midilab/aciduino/v2/docs/images/AciduinoScreens.jpg

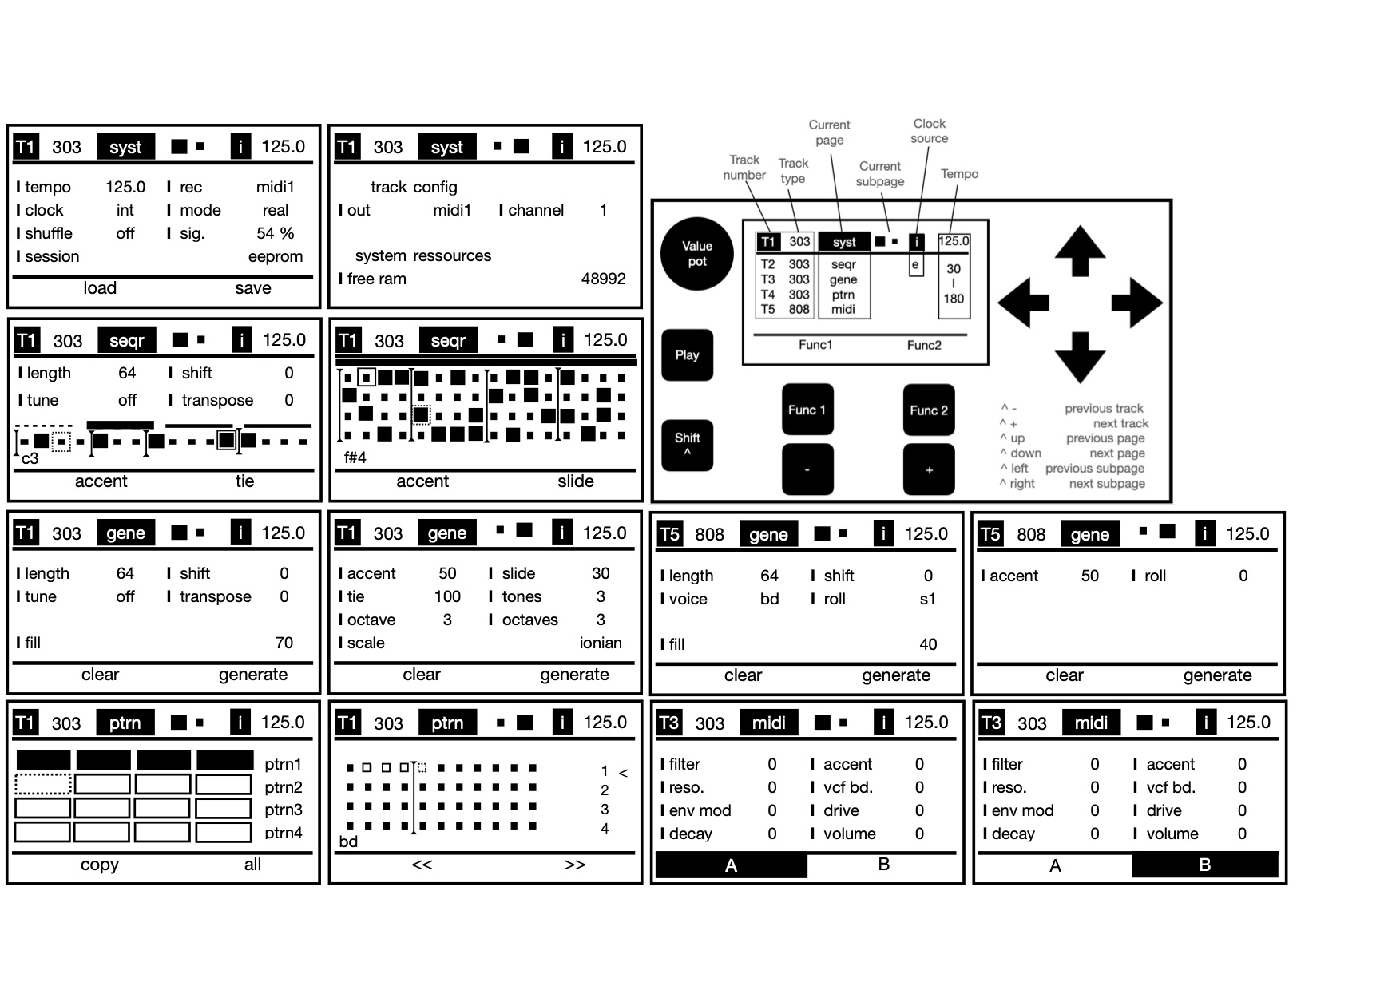
v2/docs/images/AciduinoScreens.jpg
