midilab/aciduino/v2/docs/images/BasicControls.png

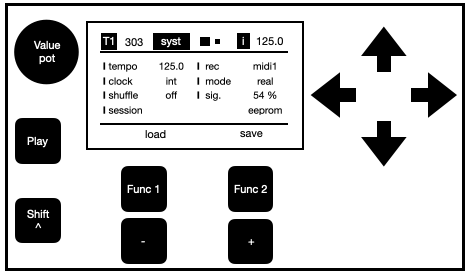
v2/docs/images/BasicControls.png
