midilab/aciduino/v2/hardware/HugoEscalpelo-3DCase-1.3inOLED-ESP32DevKitV1/Circuit/Schematic.png

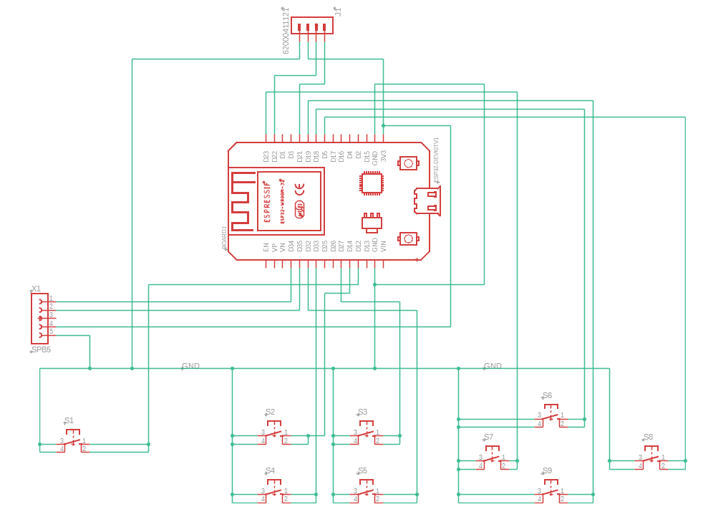
v2/hardware/HugoEscalpelo-3DCase-1.3inOLED-ESP32DevKitV1/Circuit/Schematic.png
