midilab/aciduino/v2/hardware/HugoEscalpelo-3DCase-1.3inOLED-ESP32DevKitV1/img/90x150mm-universal-pcb.jpg

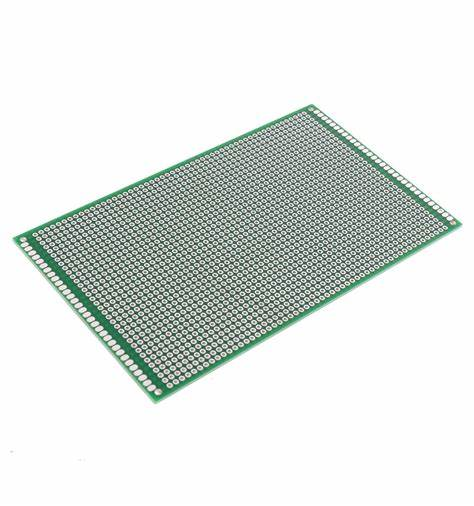
v2/hardware/HugoEscalpelo-3DCase-1.3inOLED-ESP32DevKitV1/img/90x150mm-universal-pcb.jpg
