midilab/aciduino/v2/hardware/HugoEscalpelo-3DCase-1.3inOLED-ESP32DevKitV1/img/ESP32 DevKit V1.jpg

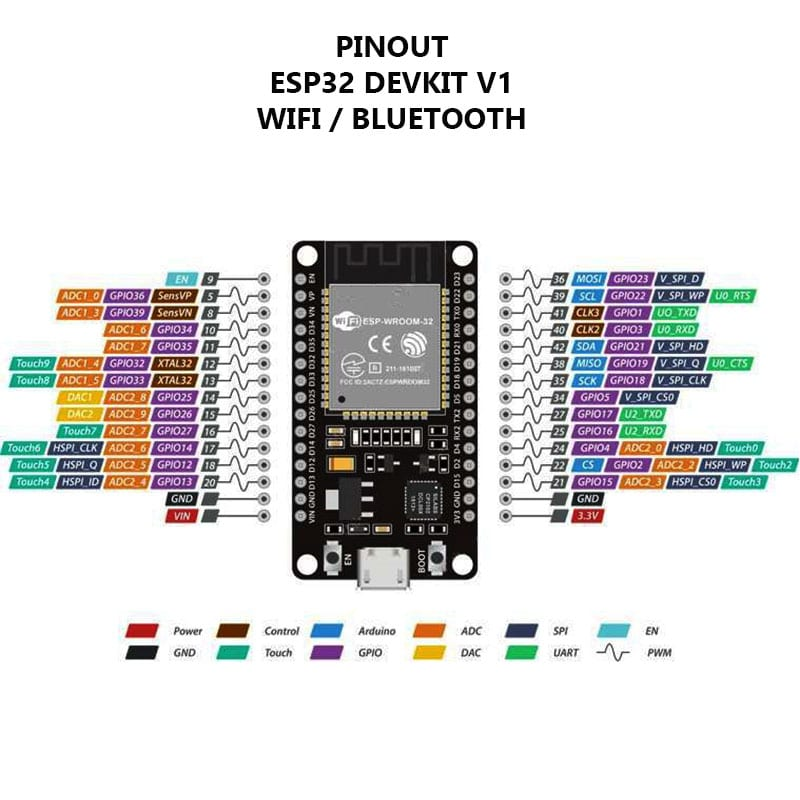
v2/hardware/HugoEscalpelo-3DCase-1.3inOLED-ESP32DevKitV1/img/ESP32 DevKit V1.jpg
