midilab/aciduino/v2/hardware/HugoEscalpelo-3DCase-1.3inOLED-ESP32DevKitV1/img/Female-heade-4pin.jpg

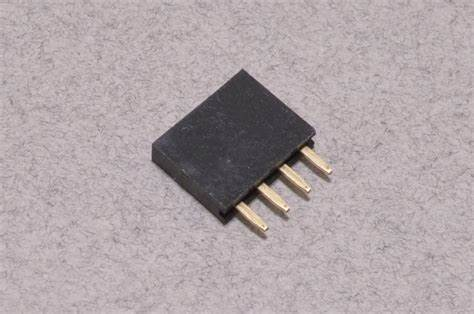
v2/hardware/HugoEscalpelo-3DCase-1.3inOLED-ESP32DevKitV1/img/Female-heade-4pin.jpg
