midilab/aciduino/v2/hardware/HugoEscalpelo-3DCase-1.3inOLED-ESP32DevKitV1/img/Keyes-rotary-encoder.jpg

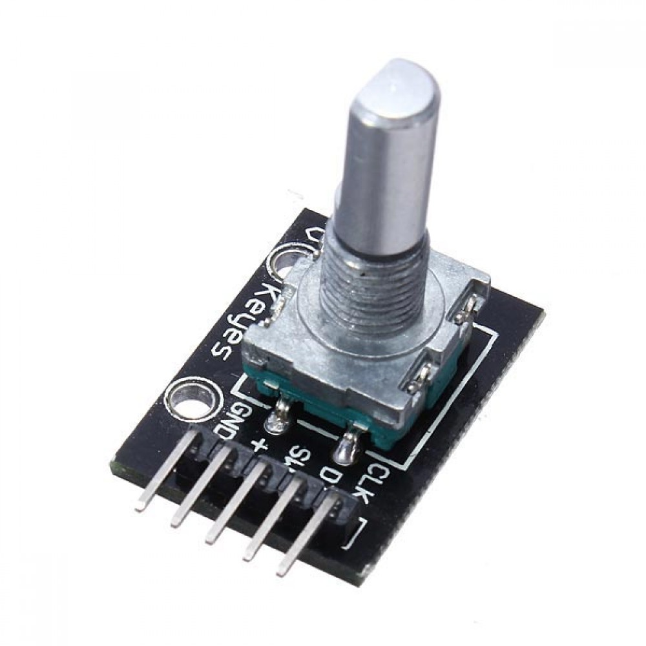
v2/hardware/HugoEscalpelo-3DCase-1.3inOLED-ESP32DevKitV1/img/Keyes-rotary-encoder.jpg
