midilab/aciduino/v2/hardware/HugoEscalpelo-3DCase-2.4inOLED-ESP32DevKitV1/img/2.14in-i2c-128x64-oled.png

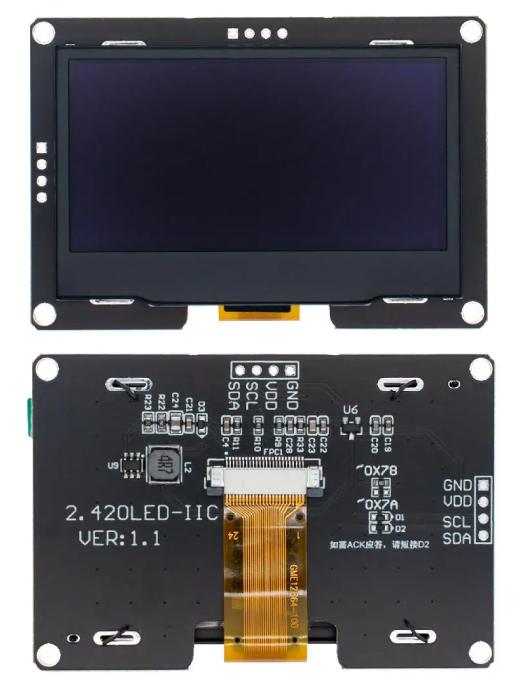
v2/hardware/HugoEscalpelo-3DCase-2.4inOLED-ESP32DevKitV1/img/2.14in-i2c-128x64-oled.png
