midilab/aciduino/v2/hardware/HugoEscalpelo-3DCase-2.4inOLED-ESP32DevKitV1/img/M2x8-screw.jpg

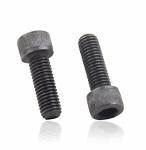
v2/hardware/HugoEscalpelo-3DCase-2.4inOLED-ESP32DevKitV1/img/M2x8-screw.jpg
