midilab/aciduino/v2/hardware/imgs/aciduinov2-lite-uone.jpg

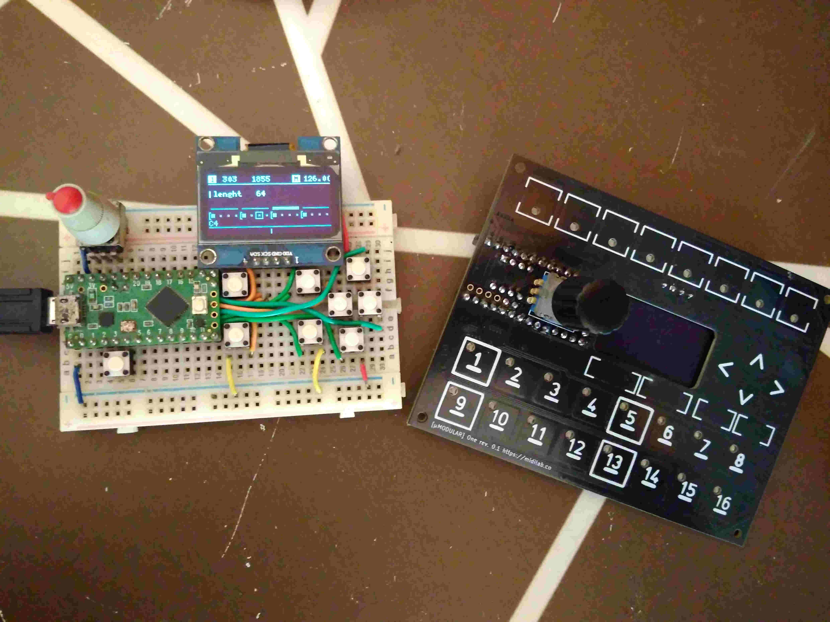
v2/hardware/imgs/aciduinov2-lite-uone.jpg
