midilab/aciduino/v2/hardware/imgs/aciduinov2-lite.jpg

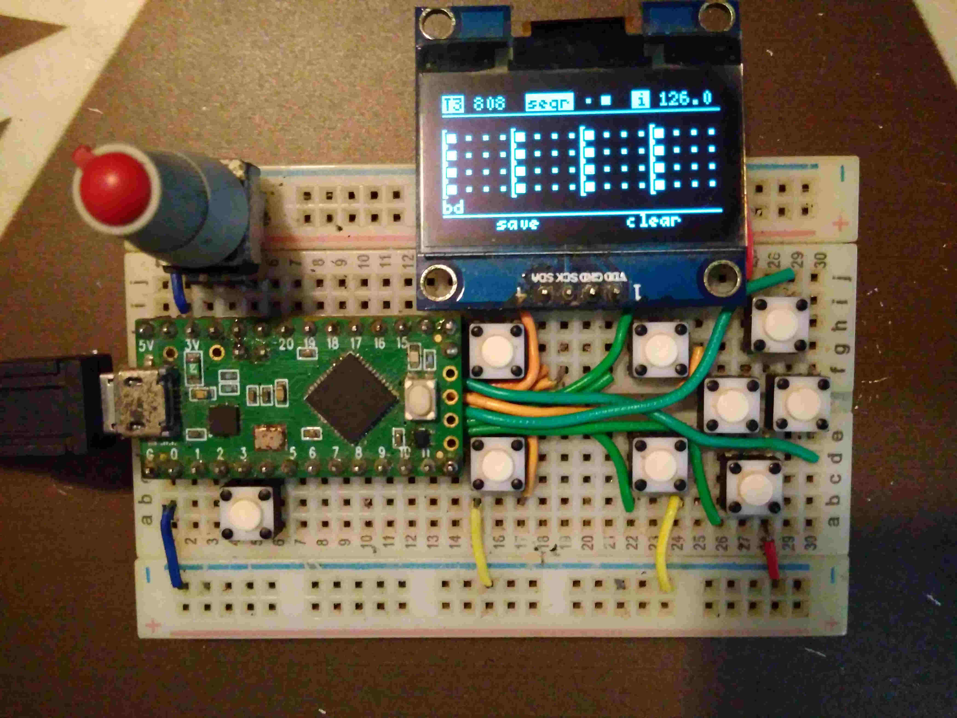
v2/hardware/imgs/aciduinov2-lite.jpg
