midilab/aciduino/v2/hardware/HugoEscalpelo-3DCase-2.4inOLED-ESP32DevKitV1/Assembly/IMG_20240221_184632.jpg

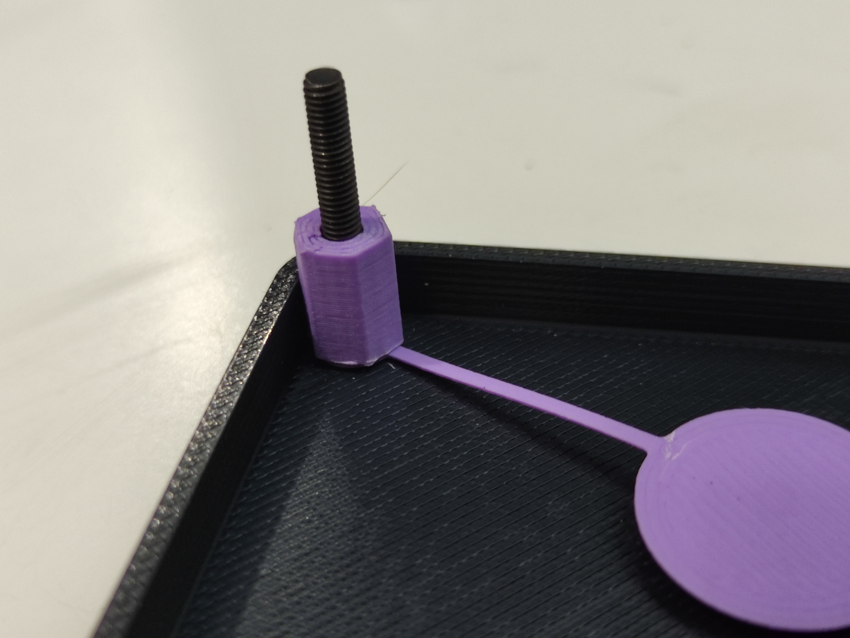
v2/hardware/HugoEscalpelo-3DCase-2.4inOLED-ESP32DevKitV1/Assembly/IMG_20240221_184632.jpg
