midilab/aciduino/v2/hardware/HugoEscalpelo-3DCase-1.3inOLED-ESP32DevKitV1/Circuit/Aciduino_Schematic_v6.sch

## EAGLE design v2/hardware/HugoEscalpelo-3DCase-1.3inOLED-ESP32DevKitV1/Circuit/Aciduino_Schematic_v6.sch (2024-02-22)

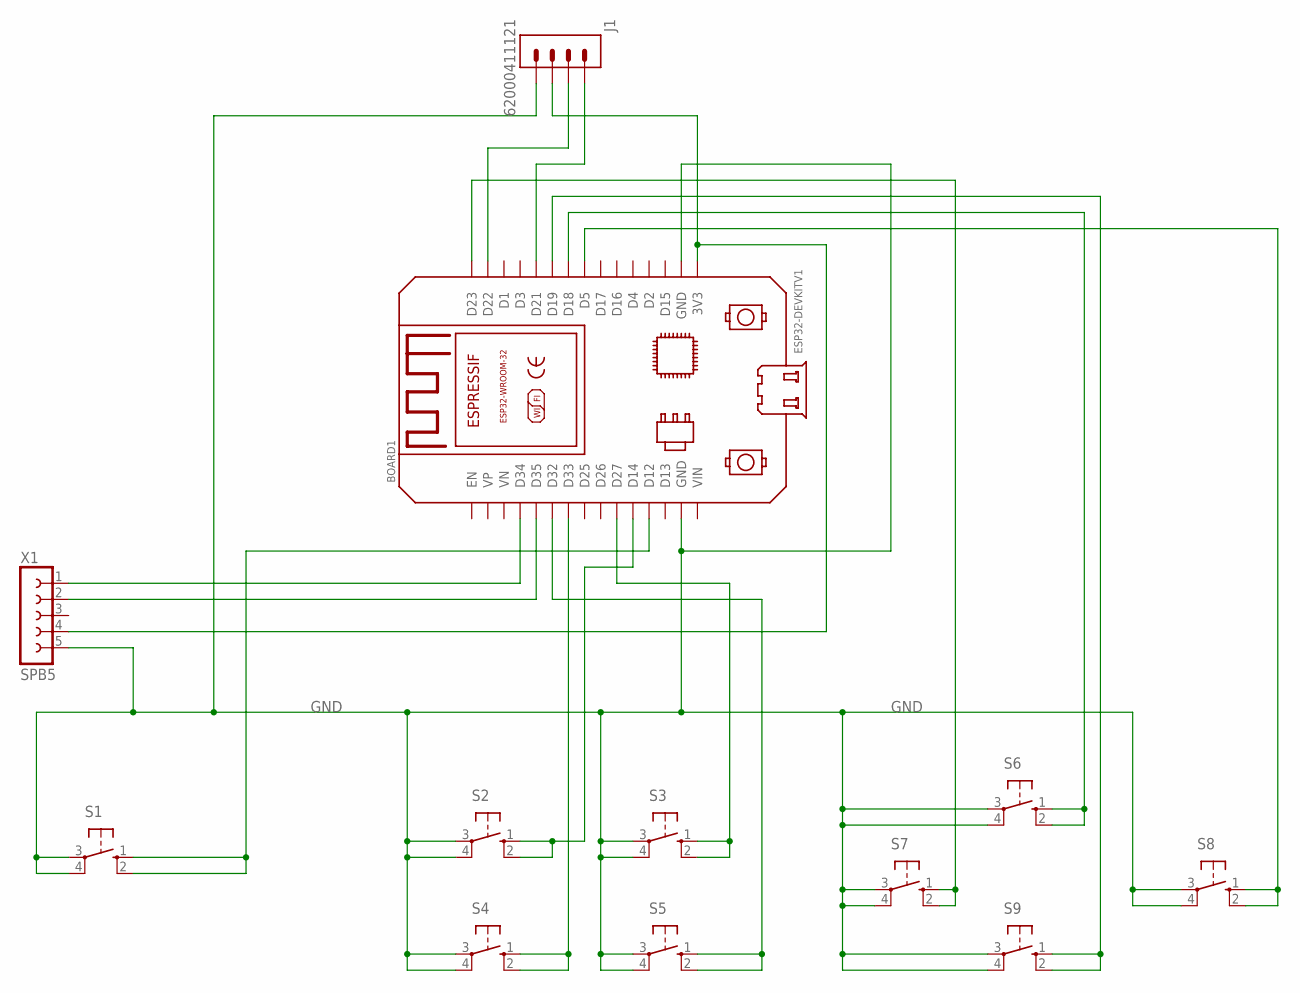
[picture p61: schematic Aciduino_Schematic_v6.sch]

Parts:
BOARD1: ESP32DEVKITV1SHRIDATTDUDHAT; ESP32-DEVKITV1
J1: 62000411121
S1, S2, S3, S4, S5, S6, S7, S8, S9: 10-XX; B3F-10XX
X1: SPB5

Connections:
GND: BOARD1.GND, BOARD1.GND@1 (GND), J1.4, S1.3, S1.4 (P1), S2.3, S2.4 (P1), S3.3, S3.4 (P1), S4.3, S4.4 (P1), S5.3, S5.4 (P1), S6.3, S6.4 (P1), S7.3, S7.4 (P1), S8.3, S8.4 (P1), S9.3, S9.4 (P1), X1.5
unnamed: BOARD1.D12, S1.1 (S), S1.2 (S1)
unnamed: BOARD1.D14, S2.1 (S), S2.2 (S1)
unnamed: BOARD1.D21, J1.1
unnamed: BOARD1.D27, S3.1 (S), S3.2 (S1)
unnamed: BOARD1.D33, S4.1 (S), S4.2 (S1)
unnamed: BOARD1.D32, S5.1 (S), S5.2 (S1)
unnamed: BOARD1.D5, S8.1 (S), S8.2 (S1)
unnamed: BOARD1.D18, S6.1 (S), S6.2 (S1)
unnamed: BOARD1.D19, S9.1 (S), S9.2 (S1)
unnamed: BOARD1.D23, S7.1 (S), S7.2 (S1)
unnamed: BOARD1.3V3, J1.3, X1.4
unnamed: BOARD1.D34, X1.1
unnamed: BOARD1.D35, X1.2
unnamed: BOARD1.D22, J1.2
