midilab/aciduino/v2/AciduinoV2/src/aciduino.cpp

#include "aciduino.hpp"

//
// setup and runtime
//
void Aciduino::init() {
  // setup clock system
  uClockSetup();
  // init the sequencer
  initSequencer();

  // force initializatiron of mute pattern data
  for (uint8_t i=0; i < 4; i++) {
    for (uint8_t j=0; j < TRACK_NUMBER_808; j++) {
      _mute_grid[i].map_808[j] = 0xFFFF;
    }
  }
}

void Aciduino::run() {
  // let uCtrl do his job
  uCtrl.run();
}

//
// Sequencer initialization
//
void Aciduino::initSequencer()
{
  // storage setup epprom/sdcard
  storageSetup();

  // init default track output data
  for(uint8_t track=0; track < TRACK_NUMBER_303+TRACK_NUMBER_808; track++) {
    _track_output_setup[track].output = MIDI_OUTPUT;
    _track_output_setup[track].channel = track;
    _track_output_setup[track].port = 0;
  }
  
  // the acid sequencer main output callback
  aciduino.seq.setOutputCallback(sequencerOutHandler);

  // we're going to init epprom in two cases:
  // if track layout changes || if no aciduino data present at epprom
  // so if you want to keep your pattenrs and change layout consider backup pattenrs into another sequencer
  // because they will be wipeout for the new memory layout to take place
  if (checkEppromDataLayoutChange()) {
    eppromInit();
  }

  // load shuffle form memory pattern?
  int8_t init_template[2] = {0,0};
  uClock.setShuffleTemplate(init_template, 2);

  // load epprom saved session
  loadSession();
  // load first pattern
  loadPattern(0);
}

void Aciduino::uClockSetup()
{
  // Inits the clock
  uClock.init();
  
  // Set the callback function for the step sequencer on 96PPQN and for step sequencer feature
  uClock.setOnPPQN(Aciduino::onPPQNCallback);
  uClock.setOnStep(Aciduino::onStepCallback);
  // Set the callback function for the clock output to send MIDI Sync message.
  uClock.setOnSync24(Aciduino::onSync24Callback);
  // Set the callback function for MIDI Start and Stop messages.
  uClock.setOnClockStart(Aciduino::onClockStart);  
  uClock.setOnClockStop(Aciduino::onClockStop);
  
  // Set the clock BPM to 126 BPM
  uClock.setTempo(126);
  //uClock.setMode(uClock.EXTERNAL_CLOCK);
}

void Aciduino::storageSetup()
{
  //
  // initiate epprom memory layout setup
  //
#if defined(ARDUINO_ARCH_ESP32) || defined(ESP32)
  _epprom_size = 4096;
#else
  _epprom_size = EEPROM.length();
#endif

  _epprom_check_data_address = 0;
  _epprom_session_address = 2;
  _epprom_session_size =(sizeof(_generative_303) + sizeof(_generative_808) + sizeof(_control_map_global) + sizeof(_track_output_setup));
  
  //
  // common pattern data definitions
  //
  _pattern_303_track_size = aciduino.seq.get303PatternTrackSize();
  _pattern_808_track_size = aciduino.seq.get808PatternTrackSize();
  _pattern_303_mem_size = aciduino.seq.get303PatternMemorySize();
  _pattern_808_mem_size = aciduino.seq.get808PatternMemorySize();
  _pattern_total_mem_size = (_pattern_303_mem_size + _pattern_808_mem_size + sizeof(_mute_grid));
  _eprrom_pattern_address = (_epprom_session_address + _epprom_session_size);
  _eprrom_pattern_available = (_epprom_size-_epprom_session_size-_epprom_session_address) / (_pattern_total_mem_size);
}

uint16_t Aciduino::getNumOfPatterns() {
  return _eprrom_pattern_available;
}

uint16_t Aciduino::getSessionSize() {
  return _epprom_session_size;
}

uint16_t Aciduino::getStorageSize() {
  return _epprom_size;
}

//
// Main interface
//
void Aciduino::playStop()
{
  if (aciduino.isPlaying())
    aciduino.stop();
  else
    aciduino.play();
}

void Aciduino::play()
{
  uClock.start();
}

void Aciduino::stop()
{
  uClock.stop();
}

void Aciduino::recToggle()
{
  aciduino.seq.setRecStatus(!aciduino.seq.getRecStatus());
}

void Aciduino::previousTrack()
{
  if (aciduino._selected_track == 0) {
    aciduino._selected_track = aciduino.seq.getTrackNumber() - 1;
  } else {
    aciduino._selected_track -= 1;
  }
}

void Aciduino::nextTrack()
{
  if (aciduino._selected_track == aciduino.seq.getTrackNumber() - 1) {
    aciduino._selected_track = 0;
  } else {
    aciduino._selected_track += 1;
  }
}

// 
// Pattern Grids
//
// MUTE GRID
uint8_t Aciduino::getMuteGridState(uint8_t mute_pattern, uint8_t track, uint8_t voice)
{
  // 303
  if (aciduino.seq.is303(track)) {
    return GET_BIT(_mute_grid[mute_pattern].map_303, track);
  // 808
  } else {
    return GET_BIT(_mute_grid[mute_pattern].map_808[track-TRACK_NUMBER_303], voice);
  }
}

void Aciduino::setMuteGridState(uint8_t mute_pattern, uint8_t state, uint8_t track, uint8_t voice)
{
  if (state == 0) {
    if (seq.is303(track)) {
      CLR_BIT(_mute_grid[mute_pattern].map_303, track);
    } else {
      CLR_BIT(_mute_grid[mute_pattern].map_808[track-TRACK_NUMBER_303], voice);
    }
  } else if (state == 1) {
    if (seq.is303(track)) {
      SET_BIT(_mute_grid[mute_pattern].map_303, track);
    } else {
      SET_BIT(_mute_grid[mute_pattern].map_808[track-TRACK_NUMBER_303], voice);
    }
  }
}
// PATTERN GRID
uint8_t Aciduino::getPatternGrid(uint8_t track)
{
  return _pattern_grid[track];
}

void Aciduino::setPatternGrid(uint8_t track, uint8_t pattern)
{
  _pattern_grid[track] = pattern;
}

//
// Generative
//
void Aciduino::generatePattern(int8_t track)
{
  uint8_t track_gen = track;
  if (track == -1)
    track_gen = _selected_track;

  if (seq.is303(track_gen)) 
    aciduino.seq.acidRandomize(track_gen, _generative_303[track_gen].generative_fill, _generative_303[track_gen].accent_probability, _generative_303[track_gen].slide_probability, _generative_303[track_gen].tie_probability, _generative_303[track_gen].number_of_tones, _generative_303[track_gen].lower_octave*12, _generative_303[track_gen].range_octave*12);
  else
    aciduino.seq.acidRandomize(track_gen, _generative_808[track_gen-TRACK_NUMBER_303].generative_fill, _generative_808[track_gen-TRACK_NUMBER_303].accent_probability, _generative_808[track_gen-TRACK_NUMBER_303].roll_probability);
}

uint8_t Aciduino::getGenerativeParam(uint8_t param, int8_t track)
{
  uint8_t track_change = track;
  uint8_t value = 0;
  if (track == -1)
    track_change = _selected_track;

  // TODO: make it array idx safe access between 303 and 808 state access
  switch (param) {
    case GENERATIVE_FILL:
      if (seq.is303(track_change)) 
        value = _generative_303[track_change].generative_fill;
      else
        value = _generative_808[track_change-TRACK_NUMBER_303].generative_fill; 
      break;
    case GENERATIVE_ACCENT:
      if (seq.is303(track_change)) 
        value = _generative_303[track_change].accent_probability;
      else
        value = _generative_808[track_change-TRACK_NUMBER_303].accent_probability; 
      break;
    case GENERATIVE_SLIDE:
      value = _generative_303[track_change].slide_probability;
      break;
    case GENERATIVE_TIE:
      value = _generative_303[track_change].tie_probability;
      break;
    case GENERATIVE_LOWER_OCTAVE:
      value = _generative_303[track_change].lower_octave;
      break;
    case GENERATIVE_RANGE_OCTAVE:
      value = _generative_303[track_change].range_octave;
      break;
    case GENERATIVE_NUM_TONES:
      value = _generative_303[track_change].number_of_tones;
      break;
    case GENERATIVE_ROLL:
      value = _generative_808[track_change-TRACK_NUMBER_303].roll_probability; 
      break;
    default:
      break;
  }

  return value;
}

void Aciduino::setGenerativeParam(uint8_t param, uint8_t data, int8_t track)
{
  uint8_t track_change = track;
  if (track == -1)
    track_change = _selected_track;

  switch (param) {
    case GENERATIVE_FILL:
      if (seq.is303(track_change))
        _generative_303[track_change].generative_fill = data;
      else
        _generative_808[track_change-TRACK_NUMBER_303].generative_fill = data;
      break;
    case GENERATIVE_ACCENT:
      if (seq.is303(track_change))
        _generative_303[track_change].accent_probability = data;
      else
        _generative_808[track_change-TRACK_NUMBER_303].accent_probability = data;
      break;
    case GENERATIVE_SLIDE:
      _generative_303[track_change].slide_probability = data;
      break;
    case GENERATIVE_TIE:
      _generative_303[track_change].tie_probability = data;
      break;
    case GENERATIVE_LOWER_OCTAVE:
      _generative_303[track_change].lower_octave = data;
      break;
    case GENERATIVE_RANGE_OCTAVE:
      _generative_303[track_change].range_octave = data;
      break;
    case GENERATIVE_NUM_TONES:
      _generative_303[track_change].number_of_tones = data;
      break;
    case GENERATIVE_ROLL:
        _generative_808[track_change-TRACK_NUMBER_303].roll_probability = data;
      break;
    default:
      break;
  }
}

//
// Track output setup
//
uint8_t Aciduino::getTrackOutputParam(uint8_t param, int8_t track)
{
  uint8_t track_change = track;
  if (track == -1)
    track_change = _selected_track;

  switch (param) {
    case TRACK_OUTPUT:
      return _track_output_setup[track_change].output;
    case TRACK_CHANNEL:
      return _track_output_setup[track_change].channel;
    case TRACK_PORT:
      return _track_output_setup[track_change].port;
    default:
      break;
  }
}

void Aciduino::setTrackOutputParam(uint8_t param, uint8_t data, int8_t track)
{
  uint8_t track_change = track;
  if (track == -1)
    track_change = _selected_track;

  switch (param) {
    case TRACK_OUTPUT:
      ATOMIC(_track_output_setup[track_change].output = data)
      break;
    case TRACK_CHANNEL:
      ATOMIC(_track_output_setup[track_change].channel = data)
      break;
    case TRACK_PORT:
      ATOMIC(_track_output_setup[track_change].port = data)
      break;
    default:
      break;
  }
}

//
// midi controller data accessors
//
int8_t Aciduino::getMidiControlParam(uint8_t param, uint8_t idx)
{
  switch (param) {
    case MIDI_CTRL:
      return _control_map_global[idx].ctrl;
    case MIDI_TRACK:
      return (int8_t)_control_map_global[idx].track;
    default:
      break;
  }
}

void Aciduino::setMidiControlParam(uint8_t param, int8_t data, uint8_t idx)
{
  switch (param) {
    case MIDI_CTRL:
      _control_map_global[idx].ctrl = data;
      break;
    case MIDI_TRACK:
      _control_map_global[idx].track = (uint8_t)data;
      break;
    default:
      break;
  }
}

//
// Midi utils
//
// 3 realtime messages used by uClock object inside interruption
inline void Aciduino::sendMidiClock() {
  msg_interrupt.type = uctrl::protocol::midi::Clock;
  uCtrl.midi->writeAllPorts(&msg_interrupt, 1);
}

void Aciduino::sendMidiStart() {
  msg.type = uctrl::protocol::midi::Start;
  uCtrl.midi->writeAllPorts(&msg, 0);  
}

void Aciduino::sendMidiStop() {
  msg.type = uctrl::protocol::midi::Stop;
  uCtrl.midi->writeAllPorts(&msg, 0);
}

// this is used inside interruption and outside, controlled by interrupted var
void Aciduino::sendMidiCC(uint8_t cc, uint8_t value, uint8_t channel, uint8_t port, uint8_t interrupted) {
  if (interrupted) {
    msg_interrupt_pots.type = uctrl::protocol::midi::ControlChange;
    msg_interrupt_pots.data1 = cc;
    msg_interrupt_pots.data2 = value;
    msg_interrupt_pots.channel = channel;
    uCtrl.midi->write(&msg_interrupt_pots, port+1, 1);
  } else {
    msg.type = uctrl::protocol::midi::ControlChange;
    msg.data1 = cc;
    msg.data2 = value;
    msg.channel = channel;
    uCtrl.midi->write(&msg, port+1, 0);
  }
}

void Aciduino::sendNote(uint8_t note, uint8_t channel, uint8_t port, uint8_t velocity) {
  msg.data1 = note;
  msg.data2 = velocity;
  msg.channel = channel;
  
  if (velocity == 0) {
    msg.type = uctrl::protocol::midi::NoteOff;
  } else {
    msg.type = uctrl::protocol::midi::NoteOn;
  }

  uCtrl.midi->write(&msg, port+1, 0);
}

// 
// storage schema
//
void Aciduino::loadSession()
{
  // check if there is a session saved.. otherwise init one based on the defaults
  // we can use the last byte as version control
  // load session data
  uCtrl.storage->load((void*)_generative_303, sizeof(_generative_303), _epprom_session_address);
  uCtrl.storage->load((void*)_generative_808, sizeof(_generative_808));
  uCtrl.storage->load((void*)_control_map_global, sizeof(_control_map_global));
  uCtrl.storage->load((void*)_track_output_setup, sizeof(_track_output_setup));
}

void Aciduino::saveSession()
{
  // save session data
  uCtrl.storage->save((void*)_generative_303, sizeof(_generative_303), _epprom_session_address);
  uCtrl.storage->save((void*)_generative_808, sizeof(_generative_808));
  uCtrl.storage->save((void*)_control_map_global, sizeof(_control_map_global));
  uCtrl.storage->save((void*)_track_output_setup, sizeof(_track_output_setup));
}

uint16_t Aciduino::getPatternEppromAddress(uint8_t pattern, int8_t track)
{
  uint16_t pattern_address = _eprrom_pattern_address + (pattern * _pattern_total_mem_size);
  if (track != -1) {
    pattern_address += aciduino.seq.is303(track) ? _pattern_303_track_size * track : _pattern_303_mem_size + (_pattern_808_track_size * (track-TRACK_NUMBER_303));
  }
  return pattern_address;
}

void Aciduino::loadPattern(uint8_t pattern, int8_t track, int8_t to_track)
{
  uint16_t pattern_address = 0;
  
  if (track != -1) {
    // load only a track patttern
    pattern_address = getPatternEppromAddress(pattern, track);
    
    // to_track request?
    if (to_track != -1)
      track = to_track;
      
    aciduino.seq.setMute(track, true);
    aciduino.seq.clearStackNote(track);
    uCtrl.storage->load((void*)aciduino.seq.getPatternData(track), (aciduino.seq.is303(track) ? _pattern_303_track_size : _pattern_808_track_size), pattern_address);
    aciduino.seq.setMute(track, false);

    // load _mute_grid only for track?
    //...
  } else {
    // load the whole pattern for all tracks
    pattern_address = getPatternEppromAddress(pattern);
    
    // mute all before load into memory(its volatile! here a mute is enongth)
    for (uint8_t i=0; i < (TRACK_NUMBER_303+TRACK_NUMBER_808); i++) {
      aciduino.seq.setMute(i, true);
    }
    // clear all floating notes around
    aciduino.seq.clearStackNote();
    
    // get 303 whole pattern data first
    uCtrl.storage->load((void*)aciduino.seq.getPatternData(0), _pattern_303_mem_size, pattern_address);
    // then 808 whole pattern data last
    uCtrl.storage->load((void*)aciduino.seq.getPatternData(TRACK_NUMBER_303), _pattern_808_mem_size, pattern_address+_pattern_303_mem_size);

    // load _mute_grid
    uCtrl.storage->load((void*)_mute_grid, sizeof(_mute_grid), pattern_address+_pattern_303_mem_size+_pattern_808_mem_size);
    
    // unmute all loaded fresh and new pattern
    for (uint8_t i=0; i < (TRACK_NUMBER_303+TRACK_NUMBER_808); i++) {
      aciduino.seq.setMute(i, false);
    }
  }
}

void Aciduino::savePattern(uint8_t pattern, int8_t track, int8_t from_track)
{
  uint16_t pattern_address = 0;
  if (track != -1) {
    // save only a track patttern
    pattern_address = getPatternEppromAddress(pattern, track);
    
    // to_track request?
    if (from_track != -1)
      track = from_track;
      
    uCtrl.storage->save((void*)aciduino.seq.getPatternData(track), (aciduino.seq.is303(track) ? _pattern_303_track_size : _pattern_808_track_size), pattern_address);

    // save _mute_grid for a specific patern
    //...
  } else {
    // saves the whole pattern for all tracks
    pattern_address = getPatternEppromAddress(pattern);
    // save 303 whole pattern data first
    uCtrl.storage->save((void*)aciduino.seq.getPatternData(0), _pattern_303_mem_size, pattern_address);
    // then 808 whole pattern data last
    uCtrl.storage->save((void*)aciduino.seq.getPatternData(TRACK_NUMBER_303), _pattern_808_mem_size, pattern_address+_pattern_303_mem_size);
    // _mute_grid data
    uCtrl.storage->save((void *)_mute_grid, sizeof(_mute_grid), pattern_address+_pattern_303_mem_size+_pattern_808_mem_size);
  }
}

void Aciduino::saveMuteGrid(uint8_t pattern)
{
  // _mute_grid data
  uCtrl.storage->save((void*)_mute_grid, sizeof(_mute_grid), getPatternEppromAddress(pattern)+_pattern_303_mem_size+_pattern_808_mem_size);
}

// copy current track data into same or another track pattern memory
void Aciduino::copyPattern(uint8_t pattern, int8_t track)
{
    _copy_pattern = pattern;
    _copy_track = track;
}

bool Aciduino::pastePattern(uint8_t pattern, int8_t track)
{
  bool copy_memory = true;
  
  if (track == -1 || _copy_track == - 1) {
    // paste whole pattern track per track
    for (uint8_t i=0; i < aciduino.seq.getTrackNumber(); i++) {
      // update _copy_track with current track
      _copy_track = i;
      pastePattern(pattern, i);
    }
    // paste _mute_grid too!
    uCtrl.storage->save((void*)_mute_grid, sizeof(_mute_grid), getPatternEppromAddress(pattern)+_pattern_303_mem_size+_pattern_808_mem_size);
    return true;
  }

  // check if track types are different
  if (aciduino.seq.is303(_copy_track) != aciduino.seq.is303(track)) {
    // cant copy.. handle UI
    return false;
  }
  
  // copy from memory or from storage?
  if (_pattern_grid[_copy_track] == _copy_pattern) {
    // we copy from current memory data
    copy_memory = true;
  } else {
    // we copy from storage data
    copy_memory = false;
  }

  // paste to memory or to storage?
  if (_pattern_grid[track] == pattern) {
    // TODO: should we save stuffs copied to memory?
    // we paste to current memory
    if (copy_memory) {
      // if paste is from memory to memory
      aciduino.seq.setMute(track, true);
      aciduino.seq.clearStackNote(track);
      memcpy(aciduino.seq.getPatternData(track), aciduino.seq.getPatternData(_copy_track), (aciduino.seq.is303(track) ? _pattern_303_track_size : _pattern_808_track_size));
      aciduino.seq.setMute(track, false);
    } else {
      // if paste is from storage to memory
      loadPattern(_copy_pattern, _copy_track, track);
    }
  } else {
    // we paste to storage data
    if (copy_memory) {
      // if paste is from memory to storage
      savePattern(pattern, track, _copy_track);
    } else {
      // if paste is from storage to storage
      uCtrl.storage->copy(getPatternEppromAddress(_copy_pattern, _copy_track), getPatternEppromAddress(pattern, track), (aciduino.seq.is303(track) ? _pattern_303_track_size : _pattern_808_track_size));
    }
  }

  return true;
}

/*
void Engine808::setBufferTrack(uint8_t track)
{
  // copy track into buffer
  memcpy(_track_helper_buffer, _sequencer[track], sizeof(_track_helper_buffer));
}
 */

bool Aciduino::checkEppromDataLayoutChange()
{
  uint16_t pattern_size = 0;
  uCtrl.storage->load((void*)&pattern_size, sizeof(pattern_size), _epprom_check_data_address);
  if (pattern_size == _pattern_total_mem_size) {
    return false;
  } else {
    return true;
  }
}

void Aciduino::eppromInit()
{
    uint16_t pattern_size = _pattern_total_mem_size;
    // init epprom session/pattern memory
    // init all epprom slots to defaults
    saveSession();
    for (uint8_t pattern=0; pattern < _eprrom_pattern_available; pattern++) {
      savePattern(pattern);
    }
    // mark epprom first bytes with pattern size to use as a checker for layout changes
    uCtrl.storage->save((void*)&pattern_size, sizeof(pattern_size), _epprom_check_data_address);
}

#if defined(TEENSYDUINO)
extern "C" char* sbrk(int incr);
int Aciduino::freeRam() {
  char top;
  return &top - reinterpret_cast<char*>(sbrk(0));
}
#elif defined(ARDUINO_ARCH_ESP32) || defined(ESP32)
int Aciduino::freeRam () 
{
  return ESP.getFreeHeap(); 
}
#elif defined(ARDUINO_ARCH_AVR)
int Aciduino::freeRam () 
{
  extern int __heap_start, *__brkval; 
  int v; 
  return (int) &v - (__brkval == 0 ? (int) &__heap_start : (int) __brkval); 
}
#endif

// used by aciduino.seq object as callback to spill data out
void Aciduino::sequencerOutHandler(uint8_t msg_type, uint8_t note, uint8_t velocity, uint8_t track)
{
  switch(aciduino._track_output_setup[track].output) {
    case MIDI_OUTPUT:
      aciduino.midiSequencerOutHandler(msg_type, note, velocity, aciduino._track_output_setup[track].channel, aciduino._track_output_setup[track].port);
      break;
    case CV_OUTPUT:
      // soon boy...
      break;
    case GATE_OUTPUT:
      // soooooooon...
      break;
  }
}

void Aciduino::midiSequencerOutHandler(uint8_t msg_type, uint8_t byte1, uint8_t byte2, uint8_t channel, uint8_t port)
{
  msg_interrupt.type = msg_type == NOTE_ON ? uctrl::protocol::midi::NoteOn : uctrl::protocol::midi::NoteOff;
  msg_interrupt.data1 = byte1;
  msg_interrupt.data2 = byte2;
  msg_interrupt.channel = channel;
  uCtrl.midi->write(&msg_interrupt, port+1, 1);
}

// All midi interface registred thru uCtrl get incomming data thru this callback
void Aciduino::midiInputHandler(uctrl::protocol::midi::MIDI_MESSAGE * msg, uint8_t port, uint8_t interrupted) 
{
  if ( uClock.getMode() == uClock.EXTERNAL_CLOCK ) {
    // external tempo control
    switch (msg->type) {
        case uctrl::protocol::midi::Clock:
          uClock.clockMe();
          return;
 
        case uctrl::protocol::midi::Start:
          uClock.start();
          return;
  
        case uctrl::protocol::midi::Stop:
          uClock.stop();
          return;
    }  
  }

  // control goes thru selected track(no matter what channel)
  switch (msg->type) {

    //
    // Note ON/OFF
    //  
    case uctrl::protocol::midi::NoteOn:
    case uctrl::protocol::midi::NoteOff:
      aciduino.seq.input(aciduino._selected_track, msg->type == uctrl::protocol::midi::NoteOn ? NOTE_ON : NOTE_OFF, msg->data1, msg->data2, interrupted);
      break;

    //
    // Control Change
    //
    case uctrl::protocol::midi::ControlChange:

      // CC MAP Control
      switch ( msg->data1 ) {

        // Sustain Controller 64
        case 64:
          //if (_foot_pedal_rec == true) {
          //  if ( msg->data2 == 127 ) {
              //footSwitchHandle(HIGH);
          //  } else if ( msg->data2 == 0 ) {
              //footSwitchHandle(LOW);
          //  }
          //  return;
          //}
          break;
      }
      break;
      
    default:
      break;
      
  }  
}

// a port to read midi notes 1ms
void Aciduino::midiHandle() {
  //while (uCtrl.midi->read(2)) {
  //}
  uCtrl.midi->read(aciduino._midi_rec_port, 1);
}

// used by uCtrl at 250us speed to get MIDI sync input messages on time
void Aciduino::midiHandleSync() {
  if (aciduino._midi_clock_port > 0 && uClock.getMode() == uClock.EXTERNAL_CLOCK) {
    //while (uCtrl.midi->read(_midi_clock_port)) {
    //}
    uCtrl.midi->read(aciduino._midi_clock_port, 1);
  }
}

#if defined(USE_BPM_LED)
void Aciduino::handle_bpm_led(uint32_t tick)
{
  // BPM led indicator
  if ( !(tick % (96)) || (tick == 1) ) {  // first compass step will flash longer
    _bpm_blink_timer = 8;
    uCtrl.dout->write(BPM_LED, HIGH, 1);
  } else if ( !(tick % (24)) ) {   // each quarter led on
    uCtrl.dout->write(BPM_LED, HIGH, 1);
  } else if ( !(tick % _bpm_blink_timer) ) { // get led off
    uCtrl.dout->write(BPM_LED, LOW, 1);
    _bpm_blink_timer = 1;
  }
}
#endif

// keep gears synced on 24PPQN resolution
void Aciduino::onSync24Callback(uint32_t tick) 
{
  // Send MIDI_CLOCK to external gears
  aciduino.sendMidiClock();
#if defined(USE_BPM_LED)
  // led clock monitor
  handle_bpm_led(tick);
#endif
}

// The callback function wich will be called by uClock each Pulse of 96PPQN clock resolution.
void Aciduino::onPPQNCallback(uint32_t tick) 
{
  // sequencer tick
  aciduino.seq.on96PPQN(tick);
}

// The callback function wich will be called by uClock each new step event time
void Aciduino::onStepCallback(uint32_t step) 
{
  // sequencer tick
  aciduino.seq.onStep(step, uClock.getShuffleLength());
}

// The callback function wich will be called when clock starts by using Clock.start() method.
void Aciduino::onClockStart() 
{
  aciduino.sendMidiStart();
  aciduino._playing = 1;
}

// The callback function wich will be called when clock stops by using Clock.stop() method.
void Aciduino::onClockStop() 
{
  aciduino.sendMidiStop();
  // clear all tracks stack note(all floating notes off!)
  aciduino.seq.clearStackNote();
  aciduino._playing = 0;
#if defined(USE_BPM_LED)
  // force to turn bpm led off
  uCtrl.dout->write(BPM_LED, LOW);
#endif
}

// static instantiation
Aciduino aciduino;
