midilab/aciduino/v2/AciduinoV2/src/sequencer/acid_sequencer.cpp

/*!
 *  @file       acid_sequencer.cpp
 *  Project     Acid Sequencer
 *  @brief      Step Sequencer that emulates roland TX series sequencers
 *  @version    0.8.0
 *  @author     Romulo Silva
 *  @date       22/09/2022
 *  @license    MIT - (c) 2022 - Romulo Silva - contact@midilab.co
 *
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
 * THE SOFTWARE IS PROVIDED "AS IS", WITHOUT WARRANTY OF ANY KIND, EXPRESS
 * OR IMPLIED, INCLUDING BUT NOT LIMITED TO THE WARRANTIES OF MERCHANTABILITY,
 * FITNESS FOR A PARTICULAR PURPOSE AND NONINFRINGEMENT. IN NO EVENT SHALL THE
 * AUTHORS OR COPYRIGHT HOLDERS BE LIABLE FOR ANY CLAIM, DAMAGES OR OTHER
 * LIABILITY, WHETHER IN AN ACTION OF CONTRACT, TORT OR OTHERWISE, ARISING
 * FROM, OUT OF OR IN CONNECTION WITH THE SOFTWARE OR THE USE OR OTHER
 * DEALINGS IN THE SOFTWARE. 
 */

// Acid StepSequencer, 
// a modular roland classic machines sequencer engine clone
// TB303, TR808, TR909
// each module can be setup output(MIDI, CV/GATE) a page to config will be nice!

// idea for 808 roll 
// use a flag or value for note_off to get into loop inside 96ppqn call with 
// note on and off controlled until it finished the step
#include "acid_sequencer.h"

AcidSequencerClass::AcidSequencerClass()
{
#if defined(ARDUINO_ARCH_ESP32) || defined(ESP32)
	_mutex = xSemaphoreCreateMutex();
#endif
  // initing our sequencer engines
  if (TRACK_NUMBER_303 > 0) {
    //_engine303 = new Engine303();
    _engine303.init();
  }

  if (TRACK_NUMBER_808 > 0) {
    //_engine808 = new Engine808();
    _engine808.init();
  }
}

// The callback function wich will be called by uClock each Pulse of 16PPQN clock resolution. Each call represents exactly one step.
void AcidSequencerClass::onStep(uint32_t step, int8_t shuffle_lenght_ctrl) 
{
  // 303 sequencer call
  _engine303.onStepCall(step, shuffle_lenght_ctrl);
  // 808 sequencer call
  _engine808.onStepCall(step, shuffle_lenght_ctrl);
}

// The callback function wich will be called by uClock each Pulse of 96PPQN clock resolution.
void AcidSequencerClass::on96PPQN(uint32_t tick) 
{
  _tick = tick;
  // 303 clock call
  _engine303.on96PPQNCall(tick);
  // 808 clock call
  _engine808.on96PPQNCall(tick);
}

uint16_t AcidSequencerClass::get303PatternMemorySize()
{
  // size of sequencer data on ram memory, to be used as base for epprom and sdcard save
  return _engine303.getPatternMemorySize();
}

uint16_t AcidSequencerClass::get303PatternTrackSize()
{
  // size of sequencer data on ram memory, to be used as base for epprom and sdcard save
  return _engine303.getPatternTrackSize();
}

uint16_t AcidSequencerClass::get808PatternMemorySize()
{
  // size of sequencer data on ram memory, to be used as base for epprom and sdcard save
  return _engine808.getPatternMemorySize();
}

uint16_t AcidSequencerClass::get808PatternTrackSize()
{
  // size of sequencer data on ram memory, to be used as base for epprom and sdcard save
  return _engine808.getPatternTrackSize();
}

void * AcidSequencerClass::getPatternData(uint8_t track)
{
  // 303 request
  if(track < TRACK_NUMBER_303)
    return _engine303.getPatternData(track);
  // 808 request?
  else
    return _engine808.getPatternData(track-TRACK_NUMBER_303);
}

void AcidSequencerClass::clearStackNote(int8_t track)
{
  if (track == -1) {
    _engine303.clearStackNote(track);
    _engine808.clearStackNote(track);
    return;
  }
  
  // 303 request
  if(track < TRACK_NUMBER_303)
    _engine303.clearStackNote(track);
  // 808 request?
  else
    _engine808.clearStackNote(track-TRACK_NUMBER_303);
}

void AcidSequencerClass::rest(uint8_t track, uint8_t step, bool state) 
{
  // 303 request
  if(track < TRACK_NUMBER_303)
    _engine303.rest(track, step, state);
  // 808 request?
  else
    _engine808.rest(track-TRACK_NUMBER_303, step, state);
}

void AcidSequencerClass::setAccent(uint8_t track, uint8_t step, bool state) 
{
  // 303 request
  if(track < TRACK_NUMBER_303)
    _engine303.setAccent(track, step, state);
  // 808 request?
  else
    _engine808.setAccent(track-TRACK_NUMBER_303, step, state);
}

void AcidSequencerClass::setSlide(uint8_t track, uint8_t step, bool state) 
{
  // 303 request
  if(track < TRACK_NUMBER_303)
    _engine303.setSlide(track, step, state);
}

void AcidSequencerClass::setRoll(uint8_t track, uint8_t step, bool state) 
{
  // 808 request?
  if(track >= TRACK_NUMBER_303)
    _engine808.setRoll(track-TRACK_NUMBER_303, step, state);
}

void AcidSequencerClass::setRollType(uint8_t track, uint8_t type)
{
  // 808 request?
  if(track >= TRACK_NUMBER_303)
    _engine808.setRollType(track-TRACK_NUMBER_303, type);
}

uint8_t AcidSequencerClass::getRollType(uint8_t track)
{
  // 808 request?
  if(track >= TRACK_NUMBER_303)
    return _engine808.getRollType(track-TRACK_NUMBER_303);
  
  return 0;
}

bool AcidSequencerClass::stepOn(uint8_t track, uint8_t step)
{
  // 303 request
  if(track < TRACK_NUMBER_303)
    return _engine303.stepOn(track, step);

  // 808 request
  return _engine808.stepOn(track-TRACK_NUMBER_303, step);
}

bool AcidSequencerClass::accentOn(uint8_t track, uint8_t step)
{
  // 303 request
  if(track < TRACK_NUMBER_303)
    return _engine303.accentOn(track, step);

  // 808 request
  return _engine808.accentOn(track-TRACK_NUMBER_303, step);
}

bool AcidSequencerClass::slideOn(uint8_t track, uint8_t step)
{
  // 303 request
  if(track < TRACK_NUMBER_303)
    return _engine303.slideOn(track, step);

  // 808 request
  return false;
}

bool AcidSequencerClass::tieOn(uint8_t track, uint8_t step)
{
  // 303 request
  if(track < TRACK_NUMBER_303)
    return _engine303.tieOn(track, step);

  // 808 request
  return false;
}

void AcidSequencerClass::setTie(uint8_t track, uint8_t step, bool state) 
{
  // 303 request
  if(track < TRACK_NUMBER_303)
    _engine303.setTie(track, step, state);
}

bool AcidSequencerClass::rollOn(uint8_t track, uint8_t step)
{
  // 808 request
  if(track >= TRACK_NUMBER_303)
    return _engine808.rollOn(track-TRACK_NUMBER_303, step);
    
  return false;
}

void AcidSequencerClass::setStepData(uint8_t track, uint8_t step, uint8_t data)
{
  // 303 request
  if(track < TRACK_NUMBER_303)
    _engine303.setStepData(track, step, data);
  // 808 request?
  else
    _engine808.setStepData(track-TRACK_NUMBER_303, step, data);
}

uint8_t AcidSequencerClass::getStepData(uint8_t track, uint8_t step)
{
  // 303 request
  if(track < TRACK_NUMBER_303)
    return _engine303.getStepData(track, step);

  // 808 request
  return _engine808.getStepData(track-TRACK_NUMBER_303, step);
}

uint8_t AcidSequencerClass::getCurrentStep(uint8_t track)
{
  // 303 request
  if(track < TRACK_NUMBER_303)
    return _engine303.getCurrentStep(track);

  // 808 request
  return _engine808.getCurrentStep(track-TRACK_NUMBER_303);
}

uint8_t AcidSequencerClass::getTrackNumber()
{
  return TRACK_NUMBER_303 + TRACK_NUMBER_808;
}

bool AcidSequencerClass::is303(uint8_t track)
{
  if (track < TRACK_NUMBER_303) {
    return true;
  }

  return false;
}

uint16_t AcidSequencerClass::getTrackMaxLength(uint8_t track)
{
  // 303 request
  if(track < TRACK_NUMBER_303)
    return STEP_MAX_SIZE_303;

  // 808 request
  return STEP_MAX_SIZE_808;
}

uint16_t AcidSequencerClass::getTrackLength(uint8_t track)
{
  // 303 request
  if(track < TRACK_NUMBER_303)
    return _engine303.getTrackLength(track);

  // 808 request
  return _engine808.getTrackLength(track-TRACK_NUMBER_303);
}

void AcidSequencerClass::setTrackLength(uint8_t track, uint16_t length)
{
  // 303 request
  if(track < TRACK_NUMBER_303)
    _engine303.setTrackLength(track, length);  
  // 808 request?
  else
    _engine808.setTrackLength(track-TRACK_NUMBER_303, length);
}

void AcidSequencerClass::setMute(uint8_t track, uint8_t mute)
{
  // 303 request
  if(track < TRACK_NUMBER_303)
    _engine303.setMute(track, mute);  
  // 808 request?
  else
    _engine808.setMute(track-TRACK_NUMBER_303, mute);
}

void AcidSequencerClass::setMute(uint8_t track, uint8_t voice, uint8_t mute)
{
  // 808 request
  if(track >= TRACK_NUMBER_303)
    _engine808.setMute(track-TRACK_NUMBER_303, voice, mute);
}

uint8_t AcidSequencerClass::getMute(uint8_t track)
{
  // 303 request
  if(track < TRACK_NUMBER_303)
    return _engine303.getMute(track);
  // 808 request?
  else
    return _engine808.getMute(track-TRACK_NUMBER_303);
}

uint8_t AcidSequencerClass::getMute(uint8_t track, uint8_t voice)
{
  // 808 request
  if(track >= TRACK_NUMBER_303)
    return _engine808.getMute(track-TRACK_NUMBER_303, voice);
}

void AcidSequencerClass::clearTrack(uint8_t track)
{
  // 303 request
  if(track < TRACK_NUMBER_303)
    _engine303.clearTrack(track);
  // 808 request?
  else
    _engine808.clearTrack(track-TRACK_NUMBER_303);
}

int8_t AcidSequencerClass::getShiftPos(uint8_t track)
{
  // 303 request
  if(track < TRACK_NUMBER_303)
    return _engine303.getShiftPos(track);
  
  // 808 request
  return _engine808.getShiftPos(track-TRACK_NUMBER_303);
}

void AcidSequencerClass::setShiftPos(uint8_t track, int8_t shift)
{
  // 303 request
  if(track < TRACK_NUMBER_303)
    _engine303.setShiftPos(track, shift); 
  // 808 request?
  else
    _engine808.setShiftPos(track-TRACK_NUMBER_303, shift);
}

void AcidSequencerClass::setTrackVoice(uint8_t track, uint8_t voice)
{
  _engine808.setTrackVoice(track-TRACK_NUMBER_303, voice);
}

uint8_t AcidSequencerClass::getTrackVoice(uint8_t track)
{
  return _engine808.getTrackVoice(track-TRACK_NUMBER_303);
}

uint8_t AcidSequencerClass::getTrackVoiceConfig(uint8_t track)
{
  return _engine808.getTrackVoiceConfig(track-TRACK_NUMBER_303);
}

void AcidSequencerClass::setTrackVoiceConfig(uint8_t track, uint8_t note)
{
  _engine808.setTrackVoiceConfig(track-TRACK_NUMBER_303, note);
}

const char * AcidSequencerClass::getTrackVoiceName(uint8_t track, uint8_t voice)
{
  return _engine808.getTrackVoiceName(track-TRACK_NUMBER_303, voice);
}

uint8_t AcidSequencerClass::getTune(uint8_t track)
{
  return _engine303.getTune(track);
}

void AcidSequencerClass::setTune(uint8_t track, uint8_t tune)
{
  _engine303.setTune(track, tune);
}

int8_t AcidSequencerClass::getTranspose(uint8_t track)
{
  return _engine303.getTranspose(track);
}

void AcidSequencerClass::setTranspose(uint8_t track, int8_t transpose)
{
  _engine303.setTranspose(track, transpose);
}

uint8_t AcidSequencerClass::getTemperamentId()
{
  return _engine303.getTemperamentId();
}

void AcidSequencerClass::setTemperament(uint8_t temperament_id)
{
  _engine303.setTemperament(temperament_id);
}

const char * AcidSequencerClass::getTemperamentName(uint8_t temperament_id)
{
  return _engine303.getTemperamentName(temperament_id);
}

void AcidSequencerClass::setOutputCallback(void (*callback)(uint8_t msg_type, uint8_t note, uint8_t velocity, uint8_t track)) 
{
  _onEventCallback = callback;
  _engine303.setOutputCallback(callback);
  _engine808.setOutputCallback(callback);
}

void AcidSequencerClass::acidRandomize(uint8_t track, uint8_t fill, uint8_t param_1, uint8_t param_2, uint8_t param_3, uint8_t param_4, uint8_t param_5, uint8_t param_6) 
{
  // 303 request
  if(track < TRACK_NUMBER_303)
    _engine303.acidRandomize(track, fill, param_1, param_2, param_3, param_4, param_5, param_6);
  // 808 request?
  else
    _engine808.acidRandomize(track-TRACK_NUMBER_303, fill, param_1, param_2);
}

const char * AcidSequencerClass::getNoteString(uint8_t note)
{
  static char szBuffer[6];  
  uint8_t octave, interval;

  octave = floor(note/12);
  interval = floor(note%12);

  sprintf(szBuffer, "%s%d", _note_string_table[interval], octave+1);
  return szBuffer;
}

void AcidSequencerClass::setRecMode(REC_MODE rec_mode)
{
  ATOMIC(_rec_mode = rec_mode);
}

void AcidSequencerClass::setRecStatus(bool record)
{
  ATOMIC(_rec_status = record);
}

bool AcidSequencerClass::getRecStatus()
{
  return _rec_status;
}

void AcidSequencerClass::input(uint8_t track, uint8_t msg, uint8_t data1, uint8_t data2, uint8_t interrupted)
{
  bool accent = false;

  // pass message thru for live play on selected track
  if (msg == NOTE_ON) {
    // check for accent
    if (data2 >= is303(track) ? ACCENT_VELOCITY_303 : NOTE_VELOCITY_808)
      accent = true;

    // send note preview
    _onEventCallback(NOTE_ON, data1, accent ? (is303(track) ? ACCENT_VELOCITY_303 : ACCENT_VELOCITY_808) : (is303(track) ? NOTE_VELOCITY_303 : NOTE_VELOCITY_808), track);
  } else if (msg == NOTE_OFF) {
    // send note off
    _onEventCallback(NOTE_OFF, data1, 0, track);
  }

  if (_rec_status == false)
    return;

  //
  // REALTIME REC MODE with quantization
  //
  if (_rec_mode == REALTIME) {
    // quantize it at ~80%
    uint8_t quantized_step = getCurrentStep(track);
    uint32_t tick = 0;
    uint8_t quantize_factor = 0;

    ATOMIC(tick = _tick);
    quantize_factor = tick % 6;

    // 4.8 is 80%, from zero based 3.8 ~4
    // -1 on this case makes perfect for live record: 3
    if ( quantize_factor > 3 ) {
      ++quantized_step;
      // in case quantization ahead of play pointer we put this note on hold to avoid ghost notes wilhe recording
      // what to do with ghost notes???
    }

    if (msg == NOTE_ON) {

      if (is303(track)) {

        // if we have a note on waiting note off and receive a note on
        // check for slide:
        //if (_rec_realtime_ctrl != -1) {
        //  _engine303.setLongTie(track, _rec_realtime_ctrl, quantized_step);
          // send note off
        //  _onEventCallback(NOTE_OFF, _rec_realtime_note, 0, track);
        //  _rec_realtime_ctrl = -1;
        //  setSlide(track, quantized_step, true);
        //} else {
          // this controls note on/off flux to keep track of realtime notes
        //  _rec_realtime_ctrl = quantized_step;
          //_rec_realtime_note = data1;
        //}

        setStepData(track, quantized_step, data1);

        // record note in!
        rest(track, quantized_step, false);
        setAccent(track, quantized_step, accent);
        
      } else {

        // check wich voice we should record
        int8_t voice = _engine808.getTrackVoiceByNote(track-TRACK_NUMBER_303, data1);
        if (voice != -1) {
          setTrackVoice(track, voice);

          // record note in!
          rest(track, quantized_step, false);
          setAccent(track, quantized_step, accent);
        }

      }

    } else if (msg == NOTE_OFF) {

      if (is303(track)) {
        
        //if (_rec_realtime_ctrl == -1) {
        //  return;
        //}
        
        // should we set a long tie?
        //if (_rec_realtime_ctrl != quantized_step) {
        //  _engine303.setLongTie(track, _rec_realtime_ctrl, quantized_step);
        //  _rec_realtime_ctrl = -1;
        //}

      }
        
    }
    
  // STEP REC MODE
  } else {

  }

}

//AcidSequencerClass aciduino;
