midilab/aciduino/v2/AciduinoV2/name.c

#if defined(TEENSYDUINO) && defined(USB_MIDI)

#include "usb_names.h"

#define MIDI_NAME   {'a','c','i','d','u','i','n','o'}
#define MIDI_NAME_LEN  8

// Do not change this part.  This exact format is required by USB.
struct usb_string_descriptor_struct usb_string_product_name = {
        2 + MIDI_NAME_LEN * 2,
        3,
        MIDI_NAME
};

#endif
