midilab/aciduino/v2/AciduinoV2/src/interface/midilab/components/generative_tie_amount.hpp

struct TieAmount : PageComponent {
  
    void view() {
      genericOptionView("tie", String(aciduino.getGenerativeParam(GENERATIVE_TIE)), line, col, selected);
    }

    void change(int16_t data) {
      data = parseData(data, 0, 100, aciduino.getGenerativeParam(GENERATIVE_TIE));
      aciduino.setGenerativeParam(GENERATIVE_TIE, data);
    }
    
} tieAmountComponent;
