midilab/aciduino/v2/AciduinoV2/src/interface/midilab/components/system_rec_input_src.hpp

struct RecInputSource : PageComponent {
    
    void view() {
      genericOptionView("rec", String(String("midi") + aciduino.getMidiRecPort()), line, col, selected);
    }

    void change(int16_t data) {
      data = parseData(data, 1, uCtrl.midi->sizeOf(), aciduino.getMidiRecPort());
      aciduino.setMidiRecPort(data);
    }

} recInputComponent;
